alexjx/Electronic_DC_Load/code/ad5541.h

#ifndef __AD5541_H__
#define __AD5541_H__

// TODO: We should wrap the DAC and ADC too
#define AD5541_SPI_SPEED   5000000ul
#define AD5541_CODES       65536u
#define AD5541_CODE_LOW    0
#define AD5541_CODE_HIGH   65535u

class AD5541
{
private:
    uint16_t _current;
    int _cs_pin;

protected:

    void send_to_device() {
        // Send CS signal
        digitalWrite(_cs_pin, LOW);
        delayMicroseconds(1);  // datsheet only need 10ns
        SPISettings setting(AD5541_SPI_SPEED, MSBFIRST, SPI_MODE0);
        SPI.beginTransaction(setting);
        SPI.transfer16(_current);
        digitalWrite(_cs_pin, HIGH);
        SPI.endTransaction();
    }

public:
    AD5541(int cs_pin) :
        _cs_pin(cs_pin)
    {
        _current = 0;
    }

    void begin()
    {
        pinMode(_cs_pin, OUTPUT);
        digitalWrite(_cs_pin, HIGH);
    }

    void setValue(uint16_t value)
    {
        _current = value;
        send_to_device();
    }

    uint16_t getValue() __attribute__((always_inline))
    {
        return _current;
    }

};

#endif
