alexjx/Electronic_DC_Load/code/setter.h

#ifndef __SETTER_H__
#define __SETTER_H__


#include <EEPROM.h>


const int32_t INCREASE_BY[] = {
    1,
    10,
    100,
    1000,
    10000,
};

const int MAX_DIGITS = sizeof(INCREASE_BY) / sizeof(INCREASE_BY[0]);
const int32_t MIN_VALUE = 0;


template <int32_t _MAX_>
class Setter
{
private:
    int32_t _value;
    int8_t  _index;

public:
    Setter() :
        _value(0), _index(0)
    {
    }

    void change(int16_t v)
    {
        _value = constrain(_value + INCREASE_BY[_index] * (int32_t)v, MIN_VALUE, _MAX_);
    }

    void move_left()
    {
        _index = (_index + 1) % MAX_DIGITS;
    }

    void move_right()
    {
        _index = (_index - 1) % MAX_DIGITS;
        if (_index < 0) {
            _index += MAX_DIGITS;
        }
    }

    void set_position(int pos)
    {
        _index = (MAX_DIGITS - pos - 1) % MAX_DIGITS;
    }

    double as_double()
    {
        return static_cast<double>(_value) / 1000.0;
    }

    int32_t get_value()
    {
        return _value;
    }

    uint8_t current_bit()
    {
        return _index;
    }

    void save_to_eeprom(int addr)
    {
        EEPROM.put(addr, _value);
    }

    bool load_from_eeprom(int addr)
    {
        int32_t loaded_value;
        EEPROM.get(addr, loaded_value);

        if (loaded_value < MIN_VALUE || loaded_value > _MAX_) {
            _value = MIN_VALUE;
            return false;
        }

        _value = loaded_value;
        return true;
    }
};

#endif
